Wojtek120/IMU-velocity-and-displacement-measurements/img/blokowycalosc.JPG

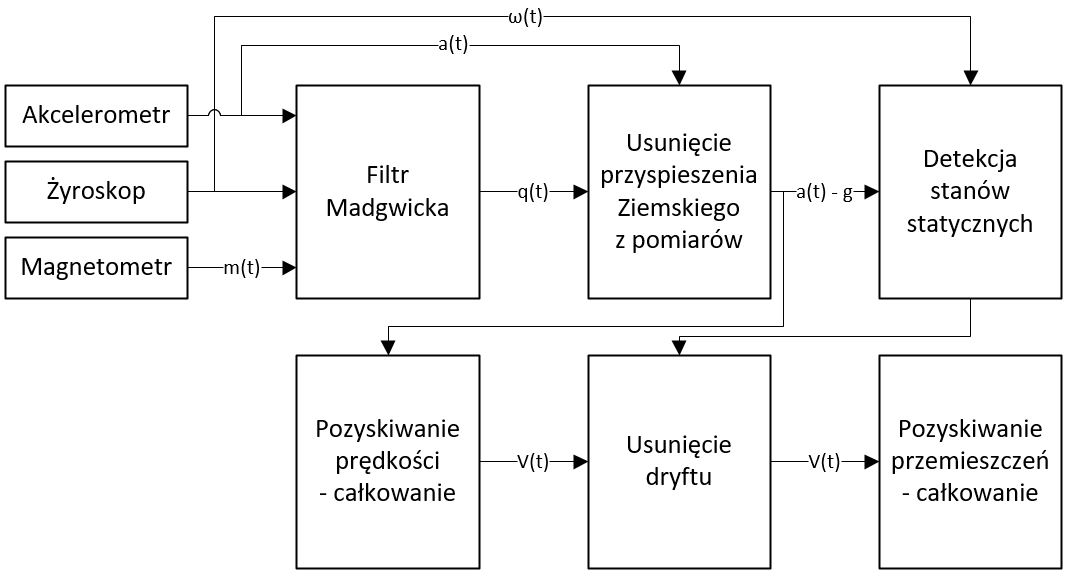
img/blokowycalosc.JPG
