Wojtek120/IMU-velocity-and-displacement-measurements/img/screen82.png

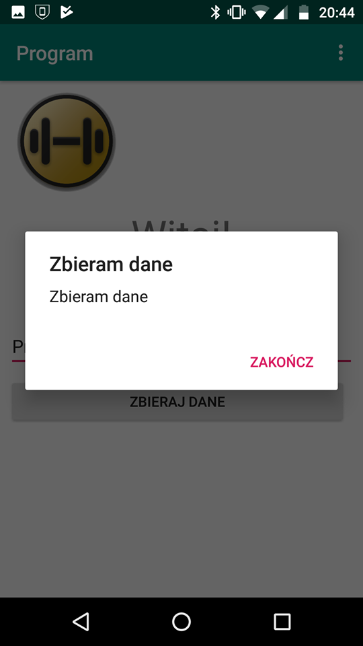
img/screen82.png
